kazushinjo/Shonan_lite-PI4/pi4/docs/images/home_illustrated_langstone.png

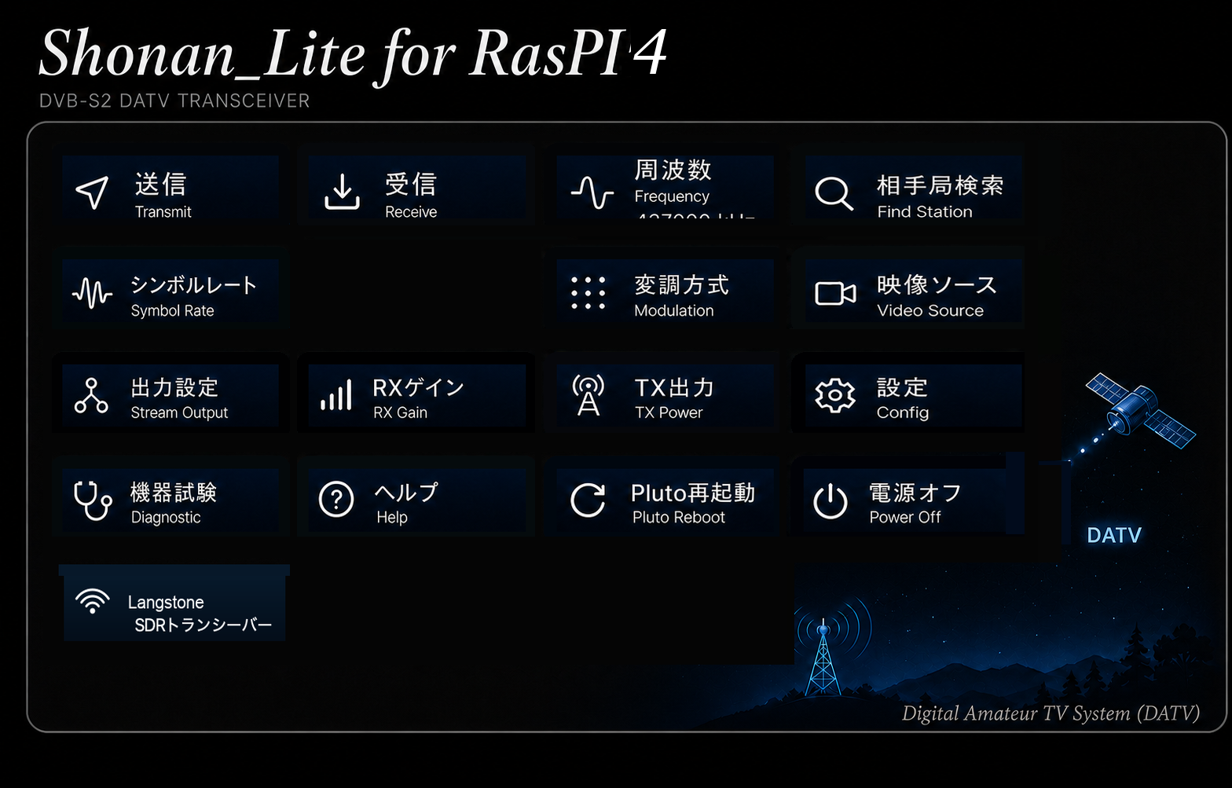
pi4/docs/images/home_illustrated_langstone.png
