kazushinjo/Shonan_lite-PI4/pi4/docs/images/home_illustrated_mockup.png

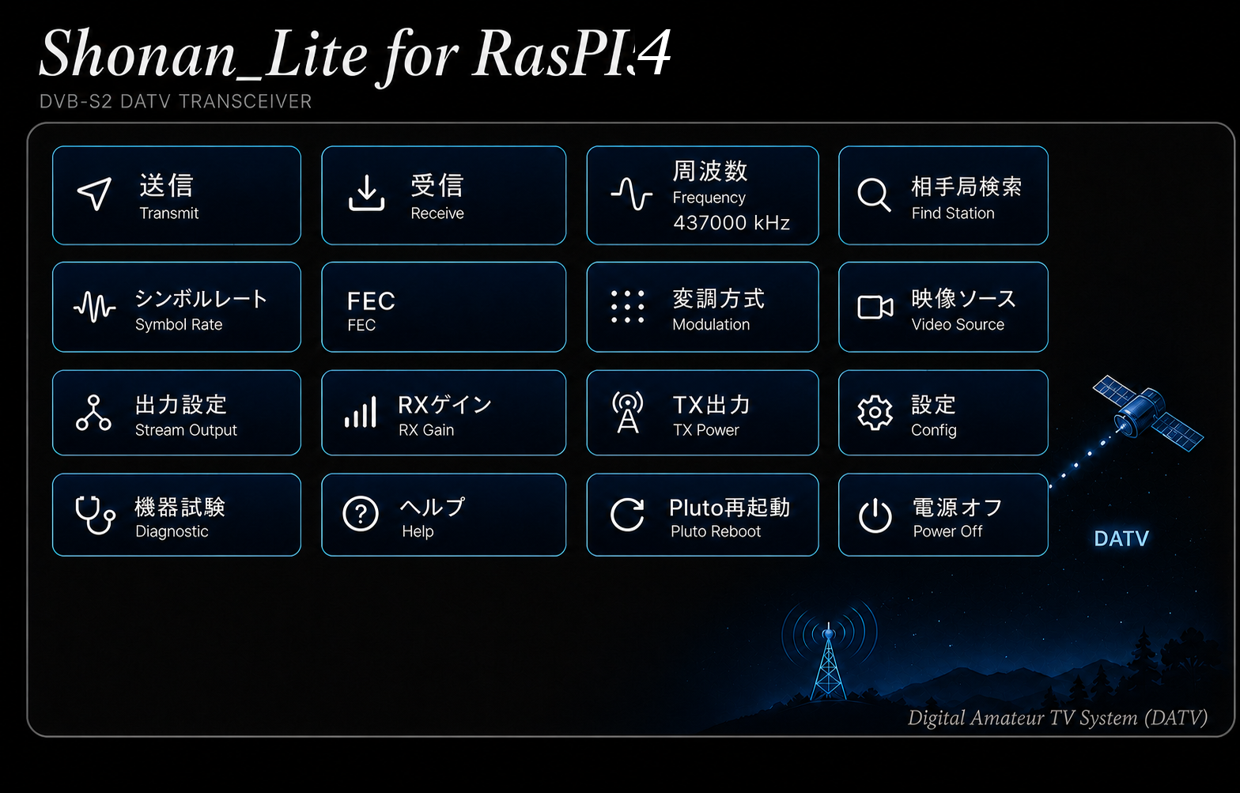
pi4/docs/images/home_illustrated_mockup.png
