kazushinjo/Shonan_lite-PI4/pi4/docs/images/screenshot_keyboard.png

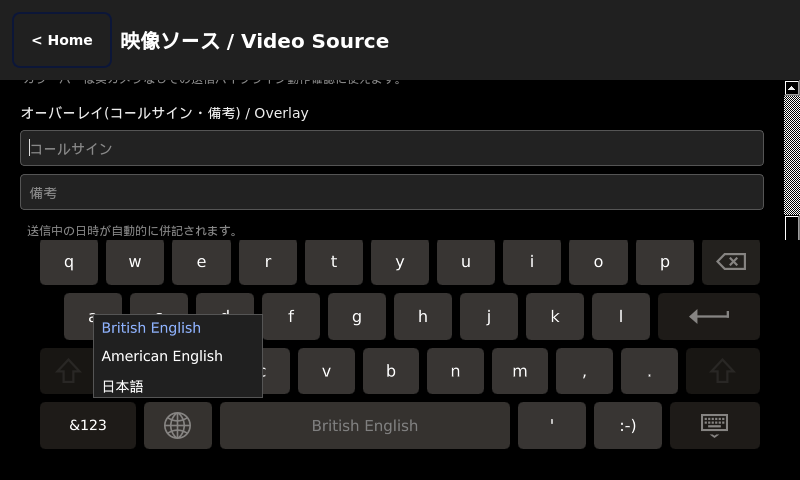
pi4/docs/images/screenshot_keyboard.png
