kazushinjo/Shonan_lite-PI4/pi4/docs/images/screenshot_overlay.png

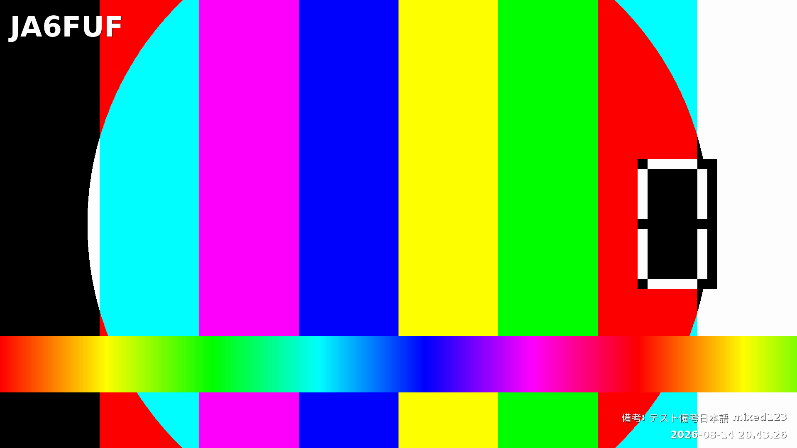
pi4/docs/images/screenshot_overlay.png
