kazushinjo/Shonan_lite-PI4/hardware/W5500_PA_PTT_Control/fabrication/assembly/w5500-esp32_3D_top_全部品.png

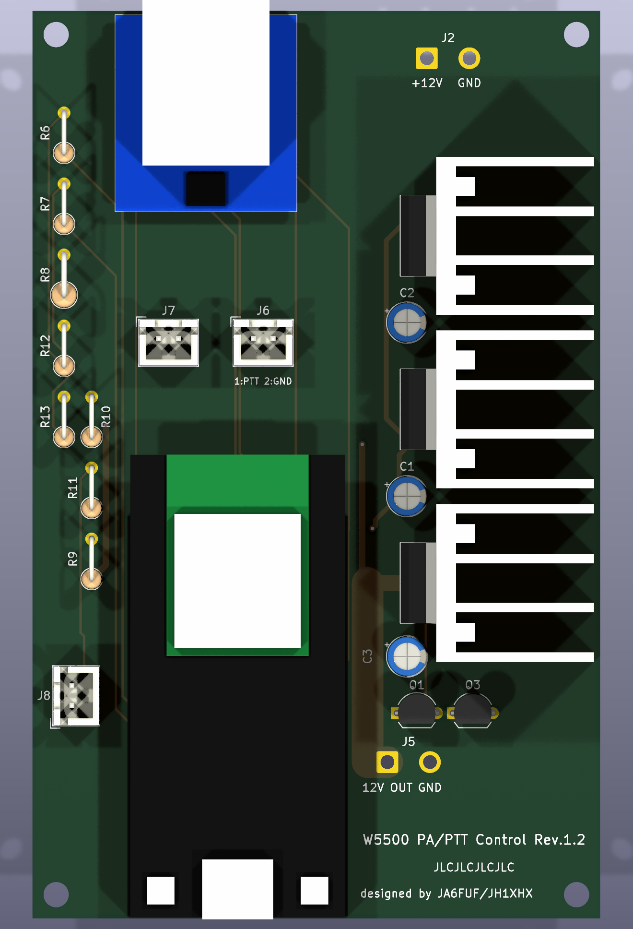
hardware/W5500_PA_PTT_Control/fabrication/assembly/w5500-esp32_3D_top_全部品.png
