kazushinjo/Shonan_lite-PI4/pi4/docs/images/test1_langstone.png

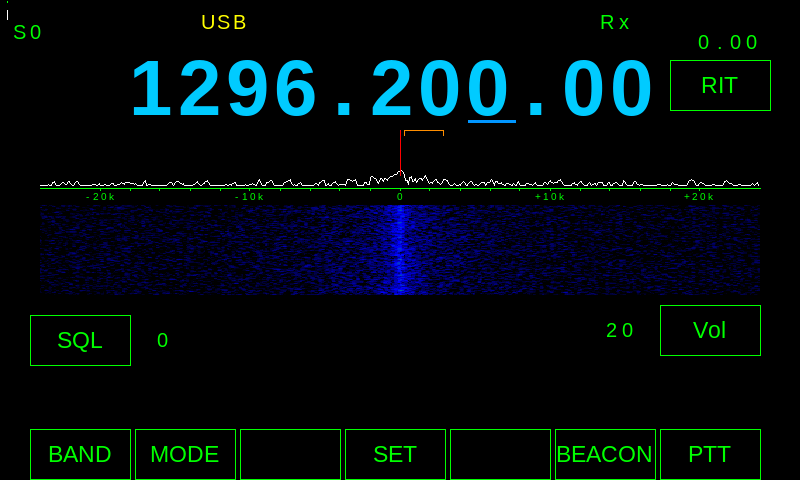
pi4/docs/images/test1_langstone.png
