kazushinjo/Shonan_lite-PI4/pi4/gui/backend.py

"""TX/RXバックエンドプロセス管理。

TX: ffmpeg映像ソース → UDP-TS(MPEG-TS over UDP、ポート8282)でPluto+上の
`udpts.sh`(`/www/settings.txt`を読み、`tsp | pluto_dvb`のパイプで変調・送出する
常駐スクリプト)へ直接プッシュする方式。開始直前にSSHで`/www/settings.txt`へ
freq/mod/sr/fec等を書き込み、udpts.shのループがそれを読み直して`pluto_dvb`を
正しいパラメータで再起動するのを待ってからffmpegを起動する。

旧SSH直接パイプ方式のコードは削除。旧`shonan_tx`(aff3ct、pi4/src/tx_main.cpp)も
GUIから呼ばない(BBHEADER CRC8の不具合が未解決のため)。

RX: shonan_rx.py(+ffplay)をQProcessで起動/停止し、標準エラー出力の状態行を
正規表現でパースしてQt Signalで通知する。
"""
from __future__ import annotations

import concurrent.futures
import http.client
import ipaddress
import os
import re
import shlex
import signal
import socket
import subprocess
import urllib.error
import urllib.request
from pathlib import Path
from typing import Optional

from PyQt5 import QtCore

from settings_store import (
    RX_SUPPORTED_MODCODS, TX_AUDIO_BITRATE_BPS, TX_SUPPORTED_MODCODS,
    TX_VIDEO_BITRATE_BPS, AppSettings,
)

PI4_DIR = Path(__file__).resolve().parent.parent  # .../pi4
# ★以前はpi4リポジトリの隣にShonan_Lite-android由来の"android"ディレクトリが
# チェックアウトされている前提のパスだったが、pi4は独立リポジトリで自己完結して
# いないと実機で参照できない(2026-08-20実機検証で発覚)。画像自体をpi4配下に
# 複製して依存を切った。
ANDROID_TEST_PATTERN = Path(__file__).resolve().parent / "assets" / "test_pattern.png"

# Pluto+上でudpts.shが`tsp -I ip 0.0.0.0:8282`として常駐待ち受けするUDP-TSポート
# (udpts.sh参照、ファームウェア固定値)。
PLUTO_UDP_TS_PORT = 8282
# PlutoのiiodがLISTENするTCPポート(ファームウェア固定値)。Windows版と同じく、
# GET /pluto.phpの200応答だけでは同一LAN上の無関係なHTTPサーバ(ルーター管理画面等)
# を誤検出するため、iiodの応答も合わせて要求して判定を厳格化する。
PLUTO_IIOD_PORT = 30431
# Windows版discover_pluto_ip()と同じ安全上限: /23より広いネットワークは
# 走査対象ホスト数が多すぎるためスキャンしない。
_DISCOVERY_MAX_SCAN_HOST_BITS = 9
# ffmpeg自身の進捗表示行("frame=  150 fps=...")の出現をもって「実際に符号化・
# 送出できている」とみなす(udpts.sh側のpluto_dvbのUnderflow等はPi4側から見えない)。
_TX_STREAMING_RE = re.compile(r"frame=\s*\d+")
# 送信画面の統計用: ffmpeg進捗行のフレーム数と、1番目の出力(UDP-TS)の累計サイズ。
# サイズを1316バイト(UDP 1パケット=TS 7パケット)で割って送出UDPパケット数とする。
_TX_PROGRESS_RE = re.compile(r"frame=\s*(\d+).*?L?size=\s*(\d+)(KiB|kB|MiB|MB|B)?")
_TX_SIZE_UNITS = {None: 1, "B": 1, "kB": 1000, "KiB": 1024, "MB": 1000 ** 2, "MiB": 1024 ** 2}
_UDP_TS_PACKET_BYTES = 1316
# 送信音声のALSAカード番号を固定値で持たない理由:
# 機体交換(046d:0825→046d:08e5)でC920がcard 0→card 1に変わった実績があり、USB抜き差しや
# 接続順序でも変わりうる(real_pluto_bringup_status.md参照)。TX開始のたびに検出する。
_CAMERA_AUDIO_ALSA_NAME_HINT = "C920"
# RX受信音声の再生に使うUSBオーディオ(カード番号はUSB抜き差しや接続順序で変わりうるため
# 固定せず、_detect_playback_alsa_device()で"USB"を含む名前から動的検出する)。
_PLAYBACK_ALSA_NAME_HINT = "USB"


def _detect_playback_alsa_device() -> Optional[str]:
    """`aplay -l`からUSBオーディオの再生カード番号を動的検出する。見つからない場合は
    Noneを返す(RX側は音声出力なしで映像のみ継続する)。"""
    try:
        result = subprocess.run(
            ["aplay", "-l"], capture_output=True, text=True, timeout=3)
    except (OSError, subprocess.TimeoutExpired):
        return None
    for line in result.stdout.splitlines():
        m = re.match(r"card (\d+):.*device (\d+):", line)
        if not m:
            continue
        if _PLAYBACK_ALSA_NAME_HINT in line:
            return f"plughw:{m.group(1)},{m.group(2)}"
    return None


def _list_capture_alsa_devices() -> list[tuple[int, str, str]]:
    """`arecord -l`の録音デバイスを(カード番号, "plughw:カード,デバイス", 行)の形で返す。"""
    try:
        result = subprocess.run(
            ["arecord", "-l"], capture_output=True, text=True, timeout=3)
    except (OSError, subprocess.TimeoutExpired):
        return []
    devices = []
    for line in result.stdout.splitlines():
        m = re.match(r"card (\d+):.*device (\d+):", line)
        if m:
            devices.append((int(m.group(1)), f"plughw:{m.group(1)},{m.group(2)}", line))
    return devices


def _usb_device_dir(sysfs_device_link: str) -> Optional[str]:
    """sysfsの`device`リンク(USBインターフェース、例: .../1-1/1-1:1.0)から、
    それが属するUSB機器のディレクトリ(.../1-1)を返す。"""
    try:
        interface_dir = os.path.realpath(sysfs_device_link)
    except OSError:
        return None
    if ":" not in os.path.basename(interface_dir):
        return None
    return os.path.dirname(interface_dir)


def _camera_alsa_card(camera_device: str, captures: list[tuple[int, str, str]]) -> Optional[int]:
    """送信に使うカメラ(v4l2)と同じUSB機器に載っている録音カードの番号を返す。

    C920は機体によって「USB PnP Sound Device」のような汎用名で列挙され、USBオーディオと
    名前で区別できないため、まずsysfs上で映像デバイスと同じUSB機器かどうかで判定し、
    分からない場合だけ名前("C920")で探す。"""
    video_name = os.path.basename(os.path.realpath(camera_device))
    camera_usb = _usb_device_dir(f"/sys/class/video4linux/{video_name}/device")
    if camera_usb is not None:
        for card, _device, _line in captures:
            if _usb_device_dir(f"/sys/class/sound/card{card}/device") == camera_usb:
                return card
    for card, _device, line in captures:
        if _CAMERA_AUDIO_ALSA_NAME_HINT in line:
            return card
    return None


def _detect_tx_audio_alsa_device(settings: AppSettings) -> Optional[str]:
    """設定画面で選んだ送信音声の入力(tx_audio_input)の録音デバイスを返す。
    camera=カメラ内蔵マイク、usb=カメラ以外の録音デバイス(USBオーディオ)。
    見つからない場合はNone(送信側は無音で送り、映像送信は中断させない)。"""
    captures = _list_capture_alsa_devices()
    camera_card = _camera_alsa_card(settings.camera_device, captures)
    for card, device, _line in captures:
        if (card == camera_card) == (settings.tx_audio_input == "camera"):
            return device
    return None


CAMERA_CAPTURE_SIZE = "1280x720"
CAMERA_CAPTURE_FPS = "30"


def _camera_input_args(device: str) -> list[str]:
    """USBカメラの入力引数。1280x720で取り込む。

    ★C920はYUYVの1280x720が最大10fpsのため、MJPEG(1280x720で30fps)があればそちらを使う。
    サイズを指定しないとC920は640x480で開くため、送信映像(1920x1080)が粗くなる。
    1280x720に対応しない汎用カメラではサイズを指定せず、ドライバ既定の解像度で開く
    (未対応のサイズ・形式を指定するとffmpegが開始できないため)。
    """
    try:
        listing = subprocess.run(
            ["v4l2-ctl", "-d", device, "--list-formats-ext"],
            capture_output=True, text=True, timeout=3).stdout
    except (OSError, subprocess.TimeoutExpired):
        listing = ""
    formats: dict[str, set[str]] = {}
    current = None
    for line in listing.splitlines():
        fmt = re.search(r"\[\d+\]: '(\w+)'", line)
        if fmt:
            current = fmt.group(1)
            formats.setdefault(current, set())
            continue
        size = re.search(r"Size: Discrete (\d+x\d+)", line)
        if size and current:
            formats[current].add(size.group(1))
    base = ["-f", "v4l2"]
    if CAMERA_CAPTURE_SIZE in formats.get("MJPG", set()):
        return base + ["-input_format", "mjpeg", "-video_size", CAMERA_CAPTURE_SIZE,
                       "-framerate", CAMERA_CAPTURE_FPS, "-i", device]
    if any(CAMERA_CAPTURE_SIZE in sizes for sizes in formats.values()):
        return base + ["-video_size", CAMERA_CAPTURE_SIZE, "-i", device]
    return base + ["-i", device]


def _set_capture_volume(device: str, percent: int) -> None:
    """録音デバイス("plughw:カード,デバイス")のマイク録音音量(ALSAミキサーの"Mic")を設定する。
    C920・USB PnP Sound Deviceとも録音音量の項目名は"Mic Capture Volume"。"""
    m = re.match(r"plughw:(\d+),", device)
    if not m:
        return
    try:
        subprocess.run(
            ["amixer", "-c", m.group(1), "sset", "Mic", f"{percent}%"],
            capture_output=True, timeout=3,
        )
    except (OSError, subprocess.TimeoutExpired):
        pass


def _audio_input_args(settings: AppSettings) -> tuple[list[str], str, Optional[str]]:
    """ffmpegの音声入力引数、ログ表示用の説明、録音デバイス(無音ならNone)を返す。

    カメラ音声・USBオーディオのどちらも1chで録音する(C920のマイク等はステレオで
    列挙されるが、plughwが1chへ変換する)。符号化側も"-ac 1"のモノラル。"""
    device = _detect_tx_audio_alsa_device(settings)
    label = "カメラ音声" if settings.tx_audio_input == "camera" else "USBオーディオ"
    if device is not None:
        return (["-f", "alsa", "-channels", "1", "-i", device],
                f"[音声] {label} ({device}、モノラル、送信音量{settings.tx_audio_volume()}%)を送信します",
                device)
    return [
        "-f", "lavfi", "-i",
        "anullsrc=channel_layout=mono:sample_rate=48000",
    ], f"[音声] {label}が見つからないため無音で送信します", None


# コールサイン/日時/備考オーバーレイに使うフォント(shonan_lite-ipad版CameraOverlayRenderer
# のPi4移植)。DejaVu Sansは英数字用、Droid Sans Fallbackは日本語用(実機で確認した限り
# 互いに相手の文字種のグリフを含まない)。drawtextフィルタは1回の呼び出しにつき
# フォントを1つしか使えないため、コールサイン・備考はPillowで事前にPNGへ文字種ごとに
# フォントを切り替えて合成し、ffmpegのoverlayフィルタで映像へ重ねる
# (_render_overlay_image/_build_overlay_pipeline参照)。日時は英数字のみなので
# 従来通りdrawtextのライブ更新(%{localtime})を使う。
_OVERLAY_FONT = "/usr/share/fonts/truetype/dejavu/DejaVuSans-Bold.ttf"
_OVERLAY_SHADOW = "shadowcolor=black@0.8:shadowx=1:shadowy=1"
_OVERLAY_ASCII_FONT_PATH = _OVERLAY_FONT
_OVERLAY_CJK_FONT_PATH = "/usr/share/fonts/truetype/droid/DroidSansFallbackFull.ttf"
_OVERLAY_IMAGE_NAME = "shonan_overlay.png"


def _split_font_runs(text: str) -> list[tuple[str, bool]]:
    """textを(区間文字列, 日本語グリフが必要か)のリストへ分割する。"""
    runs: list[tuple[str, bool]] = []
    current = ""
    current_is_cjk: Optional[bool] = None
    for ch in text:
        is_cjk = ord(ch) >= 0x3000
        if current_is_cjk is not None and is_cjk != current_is_cjk:
            runs.append((current, current_is_cjk))
            current = ""
        current += ch
        current_is_cjk = is_cjk
    if current:
        runs.append((current, bool(current_is_cjk)))
    return runs


# 送信映像の解像度はフルHD(1920x1080)固定(Pi5版と同じ)。カメラの実キャプチャ解像度や画像ファイルの
# 寸法・縦横比に関わらず、縦横比を保って縮小/拡大し、余白は黒で埋めて1920x1080に揃える。
TX_VIDEO_WIDTH = 1920
TX_VIDEO_HEIGHT = 1080
_TX_VIDEO_SCALE_FILTER = (
    f"scale={TX_VIDEO_WIDTH}:{TX_VIDEO_HEIGHT}:force_original_aspect_ratio=decrease,"
    f"pad={TX_VIDEO_WIDTH}:{TX_VIDEO_HEIGHT}:(ow-iw)/2:(oh-ih)/2,setsar=1"
)


def _parse_color(value) -> tuple[int, int, int]:
    """"#RRGGBB"を(R, G, B)へ変換する。不正な値は白。"""
    try:
        text = str(value).lstrip("#")
        if len(text) == 6:
            return tuple(int(text[i:i + 2], 16) for i in (0, 2, 4))
    except ValueError:
        pass
    return (255, 255, 255)


def _draw_mixed_text(draw, x: int, y: int, text: str, font_size: int, align: str,
                     color: tuple[int, int, int] = (255, 255, 255)) -> None:
    """英数字と日本語が混在するtextを、区間ごとにフォントを切り替えて描画する。"""
    from PIL import ImageFont

    fonts = {
        False: ImageFont.truetype(_OVERLAY_ASCII_FONT_PATH, font_size),
        True: ImageFont.truetype(_OVERLAY_CJK_FONT_PATH, font_size),
    }
    # 影は通常黒。黒など暗い文字色では影が見えないため白っぽい影にする。
    luminance = 0.299 * color[0] + 0.587 * color[1] + 0.114 * color[2]
    shadow = (0, 0, 0, 204) if luminance >= 80 else (255, 255, 255, 204)
    runs = _split_font_runs(text)
    if align == "right":
        total_width = sum(draw.textlength(t, font=fonts[c]) for t, c in runs)
        x -= total_width
    cursor = x
    for run_text, is_cjk in runs:
        font = fonts[is_cjk]
        draw.text((cursor + 1, y + 1), run_text, font=font, fill=shadow)
        draw.text((cursor, y), run_text, font=font, fill=(*color, 255))
        cursor += draw.textlength(run_text, font=font)


def _clamp_font_size(size) -> int:
    try:
        return max(8, min(256, int(size)))
    except (TypeError, ValueError):
        return 24


def _render_overlay_image(tmp_dir: str, callsign: str, note: str,
                          callsign_size: int = 68, note_size: int = 24,
                          callsign_color: str = "#FFFFFF", note_color: str = "#FFFFFF") -> str:
    """コールサイン(左上・大)と備考(右下・小、日時のすぐ上)を1920x1080の透過PNGへ描画する。
    callsign_size/note_sizeは1920x1080上での文字サイズ(px)。"""
    from PIL import Image, ImageDraw

    img = Image.new("RGBA", (TX_VIDEO_WIDTH, TX_VIDEO_HEIGHT), (0, 0, 0, 0))
    draw = ImageDraw.Draw(img)
    if callsign:
        _draw_mixed_text(draw, 24, 24, callsign, _clamp_font_size(callsign_size), align="left",
                         color=_parse_color(callsign_color))
    if note:
        # 文字サイズに関わらず備考の下端を日時のすぐ上に揃える。
        size = _clamp_font_size(note_size)
        _draw_mixed_text(draw, TX_VIDEO_WIDTH - 24, TX_VIDEO_HEIGHT - 126 - size, note, size,
                         align="right", color=_parse_color(note_color))
    path = f"{tmp_dir}/{_OVERLAY_IMAGE_NAME}"
    img.save(path)
    return path


def _build_overlay_pipeline(
        settings: AppSettings, extra_video_filters: str = "",
        *, split_preview: bool = False) -> tuple[list[str], list[str], str, str, int]:
    """映像(カメラまたは画像ファイル)を1920x1080へ揃え、コールサイン・日時・備考を重ねる
    ffmpeg入力・フィルタ関連の引数一式を組み立てる(Shonan_Lite-RasPI5からの移植)。
    戻り値は(追加入力引数, フィルタ関連引数, 映像マップ先, プレビュー用映像マップ先, 音声入力インデックス)。
    コールサイン・備考が両方空ならオーバーレイなし(フルHDへの縮小/拡大のみ)。

    split_preview=Trueの場合、映像マップ先とプレビュー用映像マップ先に別々のラベルを返す。
    ★filter_complexの出力パッド("[vout]")は一度-mapすると消費され、送信本線とプレビュー分岐の
    2箇所で同じラベルを-mapすると"Output with label ... was already used elsewhere"で
    ffmpegが起動に失敗する。splitフィルタで複製して別ラベルを割り当てる。

    ★Pi4向けの軽量化: オーバーレイ画像(1920x1080の透過PNG)は-loopで毎フレーム読み直さず
    1枚だけ入力し、overlayのeof_action=repeatで最後のフレームを重ね続ける。Pi5版と同じ
    「-loop 1 + scale2ref」ではPi4のCPUではフルHDで0.77倍速しか出ず30fpsを保てなかったが、
    この方式では1.63倍速(実機で計測)。土台の映像は先に1920x1080へ揃えるのでscale2refは不要。

    ★時刻フォーマットはコロン("%H:%M:%S")ではなく"%H.%M.%S"を使う。drawtextの
    %{localtime\\:FORMAT}展開は最初のコロン1個だけをlocaltime関数の区切りとして
    特別扱いし、FORMAT内に更にコロンがあると引数過多の警告と共に無表示になる(実機で検証済み)。
    """
    callsign = settings.overlay_callsign.strip()
    note = settings.overlay_note.strip()
    if not callsign and not note:
        # -vfは直後の最初の出力(mpegts本線)にだけ掛かる。プレビュー分岐は"0:v"を直接-mapし、
        # 別途プレビューサイズへ縮小するので問題ない。
        video_filter = _TX_VIDEO_SCALE_FILTER
        if extra_video_filters:
            video_filter += f",{extra_video_filters}"
        return [], ["-vf", video_filter], "0:v", "0:v", 1

    image_path = _render_overlay_image(
        settings.tmp_dir, callsign, note,
        settings.overlay_callsign_font_size, settings.overlay_note_font_size,
        settings.overlay_callsign_color, settings.overlay_note_color)
    date_filter = (
        f"drawtext=fontfile={_OVERLAY_FONT}:text='%{{localtime\\:%Y-%m-%d %H.%M.%S}}':"
        f"fontsize=24:fontcolor=white:x=w-text_w-24:y=h-text_h-24:{_OVERLAY_SHADOW}"
    )
    chain = (f"[0:v]{_TX_VIDEO_SCALE_FILTER}[hd];"
             f"[hd][1:v]overlay=0:0:eof_action=repeat,{date_filter}")
    if extra_video_filters:
        chain += f",{extra_video_filters}"
    if split_preview:
        chain += "[vpre];[vpre]split=2[vout][vout2]"
        video_map, preview_map = "[vout]", "[vout2]"
    else:
        chain += "[vout]"
        video_map, preview_map = "[vout]", "[vout]"
    return ["-i", image_path], ["-filter_complex", chain], video_map, preview_map, 2


# shonan_rx.pyの標準エラー出力状態行(例: "[shonan_rx] locked=False sof=0 frame=0
# rejected=0 freq_off=0.0 packets=0 errors=0")をパースする。
_RX_STATUS_RE = re.compile(
    r"locked=(True|False) sof=(\d+) frame=(\d+) rejected=(\d+) freq_off=(-?[\d.]+) packets=(\d+) errors=(\d+)"
)
# shonan-android版RxController.ktのロック監視(500ms周期ポーリング)を参考にしつつ、
# あちらにはない「停滞したら実際にプロセスを再起動する」動作を追加(実機でRXの
# フレーム同期が固まったまま進まなくなる不具合が確認されたため)。
WATCHDOG_INTERVAL_MS = 1000
WATCHDOG_STALL_TIMEOUT_MS = 8000  # frameが8秒間進まなければ停滞とみなす


def _quote(s: str) -> str:
    return shlex.quote(s)


def _build_udp_ts_url(settings: AppSettings) -> str:
    """Pluto+上のudpts.shが`tsp -I ip 0.0.0.0:8282`で待ち受けるUDP-TS宛先URL。"""
    return f"udp://{settings.pluto_host()}:{PLUTO_UDP_TS_PORT}?pkt_size=1316"


# ---- Pluto自動検出(Shonan_Lite-RasPI5から移植) ----
def _local_ipv4_subnets() -> list[tuple[str, int]]:
    """このPi4が持つ全IPv4インタフェースの(アドレス, プレフィックス長)一覧。

    Windows版と同じくpsutilが使えれば全インタフェースを列挙するが、Pi4側も
    psutilが無い場合は、UDP connect()のトリックで既定ルートの1本
    (家庭/現場運用で一般的な/24 LANと仮定)のみを返すフォールバックになる。
    """
    try:
        import psutil
        subnets = []
        for addrs in psutil.net_if_addrs().values():
            for addr in addrs:
                if addr.family != socket.AF_INET or not addr.netmask:
                    continue
                if addr.address.startswith("127.") or addr.address.startswith("169.254."):
                    continue
                prefix = sum(bin(int(octet)).count("1") for octet in addr.netmask.split("."))
                subnets.append((addr.address, prefix))
        if subnets:
            return subnets
    except Exception:
        pass
    try:
        with socket.socket(socket.AF_INET, socket.SOCK_DGRAM) as probe:
            probe.connect(("8.8.8.8", 80))
            return [(probe.getsockname()[0], 24)]
    except OSError:
        return []


def _probe_pluto(host: str, timeout: float) -> Optional[str]:
    """GET /pluto.phpの200応答に加え、iiod待受ポート(TCP)が実際に開いている
    ことも要求し、無関係なHTTPサーバの誤検出を防ぐ(Windows版と同じ判定)。
    """
    try:
        request = urllib.request.Request(f"http://{host}/pluto.php", method="GET")
        with urllib.request.urlopen(request, timeout=timeout) as response:
            if not (200 <= response.status < 300):
                return None
    except (OSError, ValueError):
        return None
    try:
        with socket.create_connection((host, PLUTO_IIOD_PORT), timeout=timeout):
            return host
    except OSError:
        return None


def discover_pluto_ip(*, timeout: float = 0.3, max_workers: int = 64) -> Optional[str]:
    """自機の全IPv4インタフェース配下でPluto+(Web UI応答+iiod待受の両方)を探す。

    Windows版discover_pluto_ip()の移植。Pluto+はPi4の既定ルートとは別の
    USB Ethernetアダプタに直結されることもあるため、_local_ipv4_subnets()で
    得られる全サブネットを走査する。
    """
    candidates: set[str] = set()
    for local_ip, prefix_len in _local_ipv4_subnets():
        host_bits = 32 - prefix_len
        if host_bits < 1 or host_bits > _DISCOVERY_MAX_SCAN_HOST_BITS:
            prefix_len = 24  # 想定外の範囲(検出失敗/広すぎるネットワーク)は/24にフォールバック
        network = ipaddress.ip_network(f"{local_ip}/{prefix_len}", strict=False)
        candidates.update(str(ip) for ip in network.hosts() if str(ip) != local_ip)
    if not candidates:
        return None

    with concurrent.futures.ThreadPoolExecutor(max_workers=max_workers) as executor:
        results = [
            host for host in executor.map(
                lambda h: _probe_pluto(h, timeout), candidates)
            if host
        ]
    if not results:
        return None
    return min(results, key=lambda ip: ipaddress.ip_address(ip))


def check_pluto_connection(settings: AppSettings) -> tuple[bool, str]:
    """IIOコンテキスト接続だけを確認し、RF設定は変更しない。"""
    try:
        settings.pluto_host()
        result = subprocess.run(
            ["iio_info", "-u", settings.pluto_uri],
            capture_output=True, text=True, timeout=5,
        )
    except (OSError, ValueError, subprocess.TimeoutExpired) as exc:
        return False, str(exc)
    if result.returncode != 0:
        detail = (result.stderr or result.stdout).strip().splitlines()
        return False, detail[-1] if detail else f"iio_info終了コード={result.returncode}"
    return True, "IIOコンテキスト接続OK"


def _uses_software_loopback(settings: AppSettings) -> bool:
    """RFループバック指定時はPlutoへ送るため、ソフトウェアループを選ばない。"""
    return settings.is_loopback() and not settings.rf_loopback_enabled


def _push_pluto_settings(settings: AppSettings, lo_hz: float) -> None:
    """SSHでPluto+の`/www/settings.txt`へDVB-S2パラメータを書き込む。

    udpts.sh(常駐shループ)は毎周回settings.txtを読み直して`pluto_dvb`を
    正しいパラメータで再起動するため、ffmpeg側のUDP-TS送出を始める前にこれを
    呼んでおく必要がある(呼ばないとPlutoが直前の周波数/シンボルレートのまま
    変調し続け、RXが一切ロックしない)。FEC値はudpts.sh側の`pluto_dvb`引数と
    同じく"/"を除いた表記(例: "3/5"→"35")で送る。pilots/frame/rolloff等
    shonan_rx.py側にも対応する設定項目がない値は両者で固定の既定値に揃える
    (pilots=On, frame=LongFrame, rolloff=0.35)。
    """
    # 430MHz帯では438.200MHzのような小数MHzを使用するため、整数化しない。
    freq_mhz = f"{lo_hz / 1_000_000:.3f}"
    symbol_rate_ksps = round(settings.symbol_rate_msps * 1000)
    fec_field = settings.fec_rate.replace("/", "")
    power = str(int(settings.tx_power_db))
    settings_text = "".join((
        f"callsign NOCALL\n",
        f"freq {freq_mhz}\n",
        "channel Custom\n",
        "mode DVBS2\n",
        f"mod {settings.modulation_scheme}\n",
        f"sr {symbol_rate_ksps}\n",
        "srselect 2000\n",
        f"fec {fec_field}\n",
        "pilots On\n",
        "frame LongFrame\n",
        f"power {power}\n",
        "rolloff 0.35\n",
        "pcrpts 800\n",
        "patperiod 200\n",
        "h265box \ncodec \nsound \naudioinput \nremux 0\n",
        "trvlo 0\ntrvloselect 0\nprovname shonan\n",
    ))
    # Write the file directly; the firmware's save.php is intentionally not used.
    ssh_command = [
        "sshpass", "-p", "analog", "ssh",
        "-o", "StrictHostKeyChecking=accept-new",
        "-o", "ConnectTimeout=6",
        "-o", "PreferredAuthentications=password",
        "-o", "PubkeyAuthentication=no",
        f"root@{settings.pluto_host()}", "tee", "/www/settings.txt",
    ]
    result = subprocess.run(
        ssh_command, input=settings_text, capture_output=True, text=True, timeout=10)
    if result.returncode != 0:
        detail = (result.stderr or result.stdout).strip()
        raise OSError(f"Pluto設定ファイル書き込み失敗: {detail or result.returncode}")


def _send_ptt_request(host: str, state: str) -> None:
    """PA_Power/PTTコントローラ(ESP32+W5500、hardware/W5500_PA_PTT_Control)へ
    TX開始/終了を通知する(`GET /tx?state=on|off`)。Pi5版と同じ経路。

    ESP32側はこのリクエストのハンドラ内でPTT(GPIO27)のON/OFFのみを行う
    (12V電源には触れない)。未接続・応答なしの場合は例外をそのまま送出する
    (呼び出し側でログのみに握りつぶし、TX本体の動作は妨げない)。
    """
    url = f"http://{host}/tx?state={state}"
    urllib.request.urlopen(url, timeout=1.5).close()


# Pi4本体のTX出力GPIO。Langstone V2のTx Output(wiringPi 29=GPIO21=物理40番ピン、
# 送信中HIGH)と同じピンに揃え、ESP32+W5500(PA_Power/PTTコントローラ)なしでも
# PA/LNA切替用のPTT ON信号を取り出せるようにする。
PI_TX_GPIO = 21


def _set_pi_tx_gpio(on: bool) -> None:
    """Pi4本体のTX出力GPIO(PI_TX_GPIO)をHIGH(送信中)/LOW(受信)にする。

    ★ラインをclaimするとLangstone側と取り合いになる可能性があるため、ラインを
    保持しない`pinctrl set`で直接書き込む。Pi以外の環境などでpinctrlが無い・
    失敗した場合は例外をそのまま送出する(呼び出し側でログのみ)。
    """
    subprocess.run(
        ["pinctrl", "set", str(PI_TX_GPIO), "op", "dh" if on else "dl"],
        check=True, timeout=2, capture_output=True,
    )


# ESP32ファームウェア(hardware/W5500_PA_PTT_Control.ino)のPIN_OUTインデックスに対応。
PTT_CHANNEL_POWER = 0  # GPIO26: 12V電源(2SJ334ハイサイドスイッチ)
PTT_CHANNEL_PTT = 1    # GPIO27: PTT


def _send_ptt_channel_state(host: str, idx: int, state: str) -> None:
    """PA_Power/PTTコントローラ(ESP32+W5500)の個別チャンネルを明示的にON/OFFする
    (`GET /ch?idx=<idx>&state=on|off`)。

    Shonan_Lite-pi4(pi4/gui)アプリ本体の起動/終了に連動したGPIO26(12V電源、
    idx=PTT_CHANNEL_POWER)制御に使う。未接続・応答なしの場合は例外をそのまま
    送出する(呼び出し側でログのみに握りつぶす)。
    """
    url = f"http://{host}/ch?idx={idx}&state={state}"
    urllib.request.urlopen(url, timeout=1.5).close()


def _terminate_process_group(process: QtCore.QProcess, sig: int) -> None:
    """QProcess.terminate()/kill()は直接の子(bash -c '...')にしか届かず、
    パイプで繋いだffmpeg/shonan_tx等の孫プロセスには届かない(bashが死んでも
    孤児として実行され続け、送信/受信が止まらない)。start()側でsetsidを使い
    bashをプロセスグループリーダーにしているため、そのグループ全体へ送る。"""
    pid = int(process.processId())
    if pid <= 0:
        return
    try:
        os.killpg(pid, sig)
    except ProcessLookupError:
        pass


class TxController(QtCore.QObject):
    status_updated = QtCore.pyqtSignal(dict)  # {"connected": bool}
    log_line = QtCore.pyqtSignal(str)
    error = QtCore.pyqtSignal(str)
    stopped = QtCore.pyqtSignal()
    video_frame = QtCore.pyqtSignal(bytes, int, int)

    def __init__(self, parent=None):
        super().__init__(parent)
        self._process: Optional[QtCore.QProcess] = None
        self._connected = False
        self._tx_frames = 0
        self._tx_packets = 0
        self._pending_lines: list[str] = []
        self._status_dirty = False
        self._quiet_mode = False
        # ウォッチドッグ再接続用。stop()が呼ばれていないのにプロセスが
        # 終了したら再起動する。
        self._should_be_running = False
        self._last_settings: Optional[AppSettings] = None
        self._last_mode: Optional[str] = None  # "video" | "camera_audio"
        # 送信中の録音デバイス(無音送信ならNone)。送信中の送信音量変更に使う。
        self._tx_audio_device: Optional[str] = None
        self._emit_timer = QtCore.QTimer(self)
        self._emit_timer.setInterval(500)
        self._emit_timer.timeout.connect(self._flush_pending_output)
        # カメラ送信中に「実際に送出している映像」を送信画面へプレビュー表示するための
        # バッファ。TX本体のffmpegプロセス自身に2つ目の出力(rawvideo→pipe:1)を追加し、
        # 同じプロセスのstdoutから直接読む(別プロセスでFIFOを読む方式は、そのプロセスが
        # 何らかの理由で予期せず終了した際にFIFOの書き手側が永久にブロックし送信全体が
        # 止まる不具合が実機で確認されたため採用しない)。
        self._preview_buffer = bytearray()
        self._preview_width = 320
        self._preview_height = 180

    def _apply_tx_audio_volume(self, settings: AppSettings) -> None:
        if self._tx_audio_device is not None:
            _set_capture_volume(self._tx_audio_device, settings.tx_audio_volume())

    def set_tx_audio_volume(self, percent: int) -> bool:
        """送信中の録音デバイスの送信音量を即時変更する。無音送信中(デバイスなし)はFalse。"""
        if self._tx_audio_device is None:
            return False
        _set_capture_volume(self._tx_audio_device, percent)
        return True

    def is_running(self) -> bool:
        return self._process is not None and self._process.state() != QtCore.QProcess.NotRunning

    def get_status(self) -> dict:
        """quiet_mode(カメラ+音声診断)中はstatus_updatedを発行しないため、呼び出し側は
        これをポーリングして状態を読む(refresh_camera_audio_frame_counts()が併せて
        _connectedも更新する)。"""
        return {"connected": self._connected}

    def _launch_ffmpeg(self, args: list, *, output_file: Optional[str] = None,
                       preview_output: bool = False) -> None:
        proc = QtCore.QProcess(self)
        proc.setProgram("ffmpeg")
        proc.setArguments(args)
        # プレビュー分岐時だけstdoutをrawvideo、stderrを進捗ログとして分離する。
        # それ以外はffmpegの進捗表示がstderrに出るため、stdoutと合流させて一本化する。
        proc.setProcessChannelMode(
            QtCore.QProcess.SeparateChannels if preview_output
            else QtCore.QProcess.MergedChannels
        )
        # ★QProcessが既定でstdinを親と繋がった開いたままのパイプにしてしまい、
        # v4l2カメラ+ALSA同時キャプチャがそれに引きずられて断続的な不具合を起こすことが
        # 実機検証で判明した(real_pluto_bringup_status.md参照)。明示的にnullDeviceへ。
        proc.setStandardInputFile(QtCore.QProcess.nullDevice())
        if output_file:
            proc.setStandardOutputFile(output_file)
        elif preview_output:
            proc.readyReadStandardError.connect(lambda: self._on_output(proc, stderr=True))
            proc.readyReadStandardOutput.connect(lambda: self._on_preview_output(proc))
        else:
            proc.readyReadStandardOutput.connect(lambda: self._on_output(proc))
        proc.finished.connect(self._on_finished)
        proc.start()
        self._process = proc
        if not output_file:
            self._emit_timer.start()

    def start(self, settings: AppSettings) -> None:
        if self.is_running():
            return
        if not settings.tx_mod_cod_supported():
            self.error.emit(
                f"未対応のMod-Cod組み合わせです: {settings.mod_cod()}\n"
                f"対応組み合わせ: {', '.join(TX_SUPPORTED_MODCODS)}"
            )
            return
        lo_hz = settings.effective_lo_hz()
        if lo_hz is None:
            self.error.emit("周波数が未設定です(ループバック試験を選択中はFrequency画面で手動設定してください)")
            return
        if settings.lnb_active():
            self.error.emit("LNB使用中は送信できません(受信専用)。周波数画面でLNBをOFFにしてください")
            return

        self._last_settings = settings
        self._last_mode = "video"
        self._should_be_running = True
        self._connected = False
        self._tx_frames = 0
        self._tx_packets = 0
        self._pending_lines = []
        self._status_dirty = False
        self._quiet_mode = False

        if settings.use_color_bar_source or settings.video_source == "colorbar":
            # Android版ColorBarSourceと同じ1920x1080固定画像を30fpsで反復する。
            video_args = [
                "-re", "-loop", "1", "-framerate", "30",
                "-i", str(ANDROID_TEST_PATTERN),
            ]
            # ★カラーバー画像自体に既にコールサインが描かれているため焼き込まない
            # (shonan_lite-ipad版VideoSourceSettingsViewと同じ扱い)。
            overlay_input_args: list[str] = []
            overlay_filter_args: list[str] = ["-vf", _TX_VIDEO_SCALE_FILTER]
            video_map = preview_video_map = "0:v"
            audio_index = 1
        elif settings.video_source == "file" and settings.video_file_path:
            # ★選択できるのは静止画のみ(videosource.py参照)。カラーバーと同じ「-loop 1 -framerate 30」で
            # 静止画を反復送信し、カメラと同じくコールサイン・備考を重ねる(Pi5版と同じ)。
            video_args = [
                "-re", "-loop", "1", "-framerate", "30",
                "-i", settings.video_file_path,
            ]
            overlay_input_args, overlay_filter_args, video_map, preview_video_map, audio_index = \
                _build_overlay_pipeline(settings, split_preview=True)
        else:
            video_args = _camera_input_args(settings.camera_device)
            overlay_input_args, overlay_filter_args, video_map, preview_video_map, audio_index = \
                _build_overlay_pipeline(settings, split_preview=True)

        # カメラ送信中は「実際に送出している映像」を送信画面へプレビュー表示する。
        # ★プレビュー分岐は本線と別のラベル(preview_video_map)を-mapする(同じ[vout]を2回
        # -mapするとffmpegが起動に失敗する)。
        preview_enabled = settings.video_source == "camera" and not settings.use_color_bar_source
        self._preview_buffer.clear()

        video_kbps = TX_VIDEO_BITRATE_BPS // 1000
        audio_kbps = TX_AUDIO_BITRATE_BPS // 1000
        if _uses_software_loopback(settings):
            output_url = f"udp://{settings.effective_loopback_host()}:{settings.rx_listen_port}?pkt_size=1316"
        else:
            try:
                _push_pluto_settings(settings, lo_hz)
            except OSError as exc:
                self.error.emit(f"Pluto+設定送信に失敗しました: {exc}")
                return
            output_url = _build_udp_ts_url(settings)
        if settings.use_on_device_demod:
            # ★オンデバイス復調はアッテネータ経由の自己受信試験でPAを使わない。PTT ONで
            # オーディオアンプの電源が切れ、受信音を聞けなくなるため、PTTはOFFのまま送信する
            # (stop()側のOFF通知は従来どおり送り、OFFを保証する)。
            self.log_line.emit("[PTT] オンデバイス復調中のためPTTをONにせず送信します")
        else:
            try:
                _set_pi_tx_gpio(True)
            except (OSError, subprocess.SubprocessError) as exc:
                self.log_line.emit(f"[PTT] Pi4 GPIO{PI_TX_GPIO}のHIGH出力に失敗しました: {exc}")
            if settings.active_ptt_controller_host():
                try:
                    _send_ptt_request(settings.active_ptt_controller_host(), "on")
                except (OSError, urllib.error.URLError, http.client.HTTPException) as exc:
                    self.log_line.emit(f"[PTT] ESP32への送信開始通知に失敗しました: {exc}")
        # 設定画面で選んだ音声入力(カメラ音声/USBオーディオ、無ければ無音)をAACで
        # 映像と一緒に送信する(Pi5版と同じ)。
        audio_args, audio_message, self._tx_audio_device = _audio_input_args(settings)
        self._apply_tx_audio_volume(settings)
        self.log_line.emit(audio_message)
        args = video_args + overlay_input_args + audio_args + overlay_filter_args + [
            "-map", video_map, "-map", f"{audio_index}:a",
            # Raspberry Pi 4のVideoCore H.264ハードウェアエンコーダを使用する。
            # dump_extraで各キーフレームへSPS/PPSを付加し、途中視聴でも復号可能にする。
            "-c:v", "h264_v4l2m2m", "-bf", "0",
            "-bsf:v", "dump_extra=freq=keyframe",
            "-b:v", f"{video_kbps}k", "-maxrate", f"{video_kbps}k", "-bufsize", f"{video_kbps}k",
            "-g", "30", "-pix_fmt", "yuv420p",
            # 16kbpsを左右2chで分け合うと音質が落ちるため、声の送信はモノラルに固定する。
            "-c:a", "aac", "-ac", "1", "-b:a", f"{audio_kbps}k",
            "-f", "mpegts", output_url,
        ]
        if preview_enabled:
            args = args + [
                "-map", preview_video_map, "-an", "-c:v", "rawvideo", "-pix_fmt", "rgb24",
                "-s", f"{self._preview_width}x{self._preview_height}", "-r", "5",
                "-f", "rawvideo", "pipe:1",
            ]
        self._launch_ffmpeg(args, preview_output=preview_enabled)

    def _on_preview_output(self, proc: QtCore.QProcess) -> None:
        self._preview_buffer.extend(bytes(proc.readAllStandardOutput()))
        frame_size = self._preview_width * self._preview_height * 3
        while len(self._preview_buffer) >= frame_size:
            frame = bytes(self._preview_buffer[:frame_size])
            del self._preview_buffer[:frame_size]
            self.video_frame.emit(frame, self._preview_width, self._preview_height)

    def stop(self) -> None:
        self._should_be_running = False
        was_running = self.is_running()
        # ★Pi4 GPIOはローカルで軽いため、起動途中で失敗した場合もHIGHのまま
        # 残さないよう、送信中かどうかにかかわらずLOWへ戻す。
        try:
            _set_pi_tx_gpio(False)
        except (OSError, subprocess.SubprocessError) as exc:
            if was_running:
                self.log_line.emit(f"[PTT] Pi4 GPIO{PI_TX_GPIO}のLOW出力に失敗しました: {exc}")
        if was_running and self._last_settings and self._last_settings.active_ptt_controller_host():
            try:
                _send_ptt_request(self._last_settings.active_ptt_controller_host(), "off")
            except (OSError, urllib.error.URLError, http.client.HTTPException) as exc:
                self.log_line.emit(f"[PTT] ESP32への送信終了通知に失敗しました: {exc}")
        if not was_running:
            return
        # ffmpegを直接起動している(setsid/bash -cのパイプ構成をやめた)ため、QProcessの
        # terminate()/kill()がそのままffmpeg本体に届く。
        self._process.terminate()
        QtCore.QTimer.singleShot(5000, self._force_kill_if_still_running)

    def _force_kill_if_still_running(self) -> None:
        if self.is_running():
            self._process.kill()

    def _on_output(self, proc: QtCore.QProcess, *, stderr: bool = False) -> None:
        # ★行ごとにシグナルを同期発行せず、いったんバッファに溜めるだけにする
        # (start_camera_audio()実行中のquiet_modeではそもそもこのハンドラ自体を使わない)。
        # 実際の発行は_flush_pending_output()。
        channel = proc.readAllStandardError() if stderr else proc.readAllStandardOutput()
        data = bytes(channel).decode("utf-8", errors="replace")
        for line in data.splitlines():
            print(f"[tx] {line}", flush=True)
            self._pending_lines.append(line)
            if not self._connected and _TX_STREAMING_RE.search(line):
                self._connected = True
                self._status_dirty = True
            progress = _TX_PROGRESS_RE.search(line)
            if progress:
                self._tx_frames = int(progress.group(1))
                size_bytes = int(progress.group(2)) * _TX_SIZE_UNITS.get(progress.group(3), 1)
                self._tx_packets = size_bytes // _UDP_TS_PACKET_BYTES
                self._status_dirty = True

    def _flush_pending_output(self) -> None:
        if self._pending_lines:
            lines, self._pending_lines = self._pending_lines, []
            for line in lines:
                self.log_line.emit(line)
        if self._status_dirty:
            self._status_dirty = False
            self.status_updated.emit({
                "connected": self._connected,
                "packets": self._tx_packets,
                "frames": self._tx_frames,
            })

    def _on_finished(self) -> None:
        self._emit_timer.stop()
        self._flush_pending_output()
        self._process = None
        self._preview_buffer.clear()
        if self._should_be_running and self._last_settings is not None:
            settings, mode = self._last_settings, self._last_mode
            QtCore.QTimer.singleShot(500, lambda: self._restart(settings, mode))
        else:
            self.stopped.emit()

    def _restart(self, settings: AppSettings, mode: Optional[str]) -> None:
        if not self._should_be_running:
            return
        if mode == "camera_audio":
            self.start_camera_audio(settings)
        else:
            self.start(settings)

    def start_camera_audio(self, settings: AppSettings) -> None:
        """カメラ映像+USBカメラ内蔵マイク音声を実際にキャプチャしてPluto+へ送出する経路が
        健全かを確認する診断用。Android版 CameraAudioTxDiagPipeline
        (Camera/Mic→H.264/AAC→TS Mux→Dvbs2TxPipeline)のPi4移植。

        ffmpegの showinfo/ashowinfo フィルタ(1フレームごとに1行ログを出す)を使って、
        Android版のvideoFrameCount/audioFrameCountに相当する正確なフレーム数を取得する。
        """
        if self.is_running():
            return
        if not settings.tx_mod_cod_supported():
            self.error.emit(
                f"未対応のMod-Cod組み合わせです: {settings.mod_cod()}\n"
                f"対応組み合わせ: {', '.join(TX_SUPPORTED_MODCODS)}"
            )
            return
        lo_hz = settings.effective_lo_hz()
        if lo_hz is None:
            self.error.emit("周波数が未設定です")
            return
        if settings.lnb_active():
            self.error.emit("LNB使用中は送信できません(受信専用)。周波数画面でLNBをOFFにしてください")
            return

        self._last_settings = settings
        self._last_mode = "camera_audio"
        self._should_be_running = True
        self._connected = False
        self._quiet_mode = True
        self.video_frame_count = 0
        self.audio_frame_count = 0
        self._ca_log_read_offset = 0
        # ffmpegの標準出力+標準エラー(showinfo/ashowinfoのログ含む)をファイルへ落とし、
        # get_status()/refresh_camera_audio_frame_counts()呼び出し時にポーリングで読む。
        self._ca_log_path = f"{settings.tmp_dir}/shonan_ca_ffmpeg.log"

        video_kbps = TX_VIDEO_BITRATE_BPS // 1000
        audio_kbps = TX_AUDIO_BITRATE_BPS // 1000
        # H.264/AACはPi 4で符号化し、Plutoのudpts.shはUDP-TSをそのまま変調へ渡す。
        try:
            _push_pluto_settings(settings, lo_hz)
        except OSError as exc:
            self.error.emit(f"Pluto+設定送信に失敗しました: {exc}")
            return
        udp_ts_url = _build_udp_ts_url(settings)
        overlay_input_args, overlay_filter_args, video_map, _preview_video_map, audio_index = \
            _build_overlay_pipeline(settings, extra_video_filters="showinfo")
        audio_args, _audio_message, self._tx_audio_device = _audio_input_args(settings)
        self._apply_tx_audio_volume(settings)
        args = _camera_input_args(settings.camera_device) + overlay_input_args + \
            audio_args + overlay_filter_args + [
            "-map", video_map, "-map", f"{audio_index}:a",
            "-c:v", "h264_v4l2m2m", "-bf", "0",
            "-bsf:v", "dump_extra=freq=keyframe",
            "-b:v", f"{video_kbps}k", "-maxrate", f"{video_kbps}k", "-bufsize", f"{video_kbps}k",
            "-g", "30", "-pix_fmt", "yuv420p",
            "-c:a", "aac", "-ac", "1", "-b:a", f"{audio_kbps}k", "-af", "ashowinfo",
            "-f", "mpegts", udp_ts_url,
        ]
        self._launch_ffmpeg(args, output_file=self._ca_log_path)

    def refresh_camera_audio_frame_counts(self) -> None:
        """診断中に1秒おき等で呼び、ffmpegのshowinfo/ashowinfoログファイルから
        映像/音声フレーム数を数え直し(Android版videoFrameCount/audioFrameCount相当)、
        併せて_connected(ffmpeg自身の進捗行の出現)も更新する。

        ★毎回ファイル全体を読み直して数え直す実装だと、ログが数千行に育つにつれ
        Qtイベントループを塞ぐ時間が伸びる懸念があったため(real_pluto_bringup_status.md
        参照)、前回読み取り位置以降の差分のみ読んで加算する。
        """
        log_path = getattr(self, "_ca_log_path", None)
        if not log_path or not os.path.exists(log_path):
            return
        offset = getattr(self, "_ca_log_read_offset", 0)
        try:
            with open(log_path, "r", errors="replace") as f:
                f.seek(offset)
                chunk = f.read()
                self._ca_log_read_offset = f.tell()
        except OSError:
            return
        self.video_frame_count += chunk.count("Parsed_showinfo")
        self.audio_frame_count += chunk.count("Parsed_ashowinfo")
        if not self._connected and _TX_STREAMING_RE.search(chunk):
            self._connected = True


class RxController(QtCore.QObject):
    status_updated = QtCore.pyqtSignal(dict)
    log_line = QtCore.pyqtSignal(str)
    error = QtCore.pyqtSignal(str)
    stopped = QtCore.pyqtSignal()
    video_frame = QtCore.pyqtSignal(bytes, int, int)

    def __init__(self, parent=None):
        super().__init__(parent)
        self._rx_process: Optional[QtCore.QProcess] = None
        self._ffplay_process: Optional[QtCore.QProcess] = None
        self._fifo_path: Optional[str] = None
        self._settings: Optional[AppSettings] = None
        self._last_frame_count = 0
        self._ms_since_progress = 0
        self._restart_pending = False
        self._video_buffer = bytearray()
        self._video_width = 640
        self._video_height = 360
        self._watchdog_timer = QtCore.QTimer(self)
        self._watchdog_timer.setInterval(WATCHDOG_INTERVAL_MS)
        self._watchdog_timer.timeout.connect(self._check_watchdog)

    def run_iio_preflight(self, settings: AppSettings, *, notify_error: bool = True) -> bool:
        """短いDMA読出しでPluto RX/IIOの健全性を確認する。"""
        if not settings.iio_preflight_enabled:
            self.log_line.emit("[iio-preflight] SKIPPED (disabled in settings)")
            return True
        if settings.is_loopback():
            return True
        probe_cmd = (
            "set -o pipefail; "
            f"iio_readdev -u {_quote(settings.pluto_uri)} -b 32768 "
            "cf-ad9361-lpc voltage0 voltage1 2>/tmp/shonan_iio_probe.err "
            "| head -c 4096 | wc -c"
        )
        try:
            probe = subprocess.run(
                ["bash", "-c", probe_cmd], capture_output=True,
                text=True, timeout=6)
            probe_bytes = int(probe.stdout.strip() or "0")
        except (OSError, ValueError, subprocess.TimeoutExpired):
            probe_bytes = 0
        if probe_bytes >= 4096:
            self.log_line.emit(f"[iio-preflight] OK ({probe_bytes} bytes)")
            return True
        message = (
            "Pluto RX DMAのIIOプリフライトに失敗しました。"
            "RF NO LOCKではありません。Plutoを再起動してから再試行してください。"
        )
        self.log_line.emit(f"[iio-preflight] FAILED: {message}")
        if notify_error:
            self.error.emit(message)
        return False

    def is_running(self) -> bool:
        return self._rx_process is not None and self._rx_process.state() != QtCore.QProcess.NotRunning

    def start(self, settings: AppSettings) -> None:
        if self.is_running():
            return
        if not settings.rx_mod_cod_supported():
            self.error.emit(
                f"未対応のMod-Cod組み合わせです: {settings.mod_cod()}\n"
                f"対応組み合わせ: {', '.join(RX_SUPPORTED_MODCODS)}"
            )
            return
        # ★LNB使用中は表示周波数(10GHz)ではなく、LNB局部発振を引いたIF周波数で受信する。
        lo_hz = settings.rx_tune_hz()
        if lo_hz is None:
            self.error.emit("周波数が未設定です")
            return

        # Pluto単体の再起動ではPluto側の設定が初期値へ戻るため、RX先行時も
        # 開始直前にTX/RX共通パラメータを必ず再適用する。
        try:
            _push_pluto_settings(settings, lo_hz)
        except OSError as exc:
            self.error.emit(f"Pluto設定送信に失敗しました: {exc}")
            return

        if not self.run_iio_preflight(settings):
            return

        self._settings = settings
        self._last_frame_count = 0
        self._ms_since_progress = 0
        self._restart_pending = False

        fifo_path = f"{settings.tmp_dir}/shonan_rx_gui.ts"
        self._fifo_path = fifo_path

        # ★TxControllerは_push_pluto_settings()でpilots=Onを送るため、
        # RX側も--pilotsを明示してTXと一致させる。
        # ★shonan_rx.pyの--sample-rate-hzは実IQサンプルレート(sps=2固定、
        # real_pluto_bringup_status.md参照)。symbol_rate_msps由来のsymbol_rate_hz()から
        # 2倍して求める(旧settings.sample_rate_hz固定値フィールドはsymbol_rate_msps側の
        # 実制御に一本化されたため廃止)。
        sample_rate_hz = settings.symbol_rate_hz() * 2
        rx_cmd = (
            f"rm -f {_quote(fifo_path)}; mkfifo {_quote(fifo_path)}; "
            f"python3 {PI4_DIR}/rx/shonan_rx.py --pluto-uri {_quote(settings.pluto_uri)} "
            f"--lo-hz {lo_hz} --sample-rate-hz {sample_rate_hz} "
            f"--mod-cod {_quote(settings.mod_cod())} --pilots "
            f"--agc {'--agc' if settings.rx_agc_enabled else '--no-agc'} "
            f"--gain-db {settings.rx_gain_db} --output-fifo {_quote(fifo_path)} 2>&1"
        )

        proc = QtCore.QProcess(self)
        proc.setProgram("setsid")
        proc.setArguments(["bash", "-c", rx_cmd])
        # ★TxController.start()と同じ理由でstdinを明示的にnullDeviceへ
        # (real_pluto_bringup_status.md参照。RX側では未確認だが予防的に統一する)。
        proc.setStandardInputFile(QtCore.QProcess.nullDevice())
        proc.readyReadStandardOutput.connect(lambda: self._on_output(proc))
        proc.finished.connect(self._on_finished)
        proc.start()
        self._rx_process = proc
        self._watchdog_timer.start()

        # file_sink(RX側)はFIFOをwriteでopenする際、読み手が先にいないとブロックするため
        # 少し遅らせてffmpegを起動する(pi4/scripts/run_rx_display.shと同じ理由)。
        QtCore.QTimer.singleShot(1500, lambda: self._start_ffplay(fifo_path))

    def _start_ffplay(self, fifo_path: str) -> None:
        """FIFOを1つのffmpegプロセスだけで読み、映像は生RGBフレームとしてstdoutへ
        (video_frameシグナル経由でQt側QLabelへ描画)、音声はUSBオーディオへ直接出力する
        2系統出力にする。★GUI(Qt eglfs)がKMS/DRMディスプレイを既に占有しているため、
        ffplay単体をFIFOに向けて起動する方式(外部ウィンドウ表示)は、SDL2側が
        DRMマスターを取得できずダミードライバへ無言でフォールバックし、プロセスは
        生きたまま何も表示されない不具合が実機で確認された。ffmpegでRGBへ変換して
        Qt自身の描画パイプラインに乗せることでこの競合を回避する。FIFOは1プロセス
        しか安定して読めないため、映像と音声を同じffmpeg起動から分岐させる。
        ★音声出力先を汎用エイリアス"default"にするとQProcess経由で実機がクラッシュ
        した(この機体の"default"は再生に使えないデバイスへ解決されている模様)。
        音声なしのテストパターンや映像ソースでは、音声出力を同じffmpegに追加すると
        「Output file does not contain any stream」でプロセスが終了するため、表示用は
        映像出力だけにする。"""
        if self._ffplay_process is not None or self._settings is None:
            return
        self._video_buffer.clear()
        proc = QtCore.QProcess(self)
        proc.setProgram('ffmpeg')
        args = [
            '-loglevel', 'warning', '-fflags', 'nobuffer', '-flags', 'low_delay',
            '-f', 'mpegts', '-i', fifo_path,
            '-an', '-vf', f'scale={self._video_width}:{self._video_height}',
            '-pix_fmt', 'rgb24', '-f', 'rawvideo', 'pipe:1',
        ]
        proc.setArguments(args)
        proc.readyReadStandardOutput.connect(lambda: self._on_video_output(proc))
        proc.readyReadStandardError.connect(lambda: print(
            f"[video] {bytes(proc.readAllStandardError()).decode('utf-8', errors='replace').strip()}", flush=True))
        proc.errorOccurred.connect(lambda err: print(f"[video] QProcess error: {err}", flush=True))
        proc.start()
        self._ffplay_process = proc

    def _on_video_output(self, proc: QtCore.QProcess) -> None:
        self._video_buffer.extend(bytes(proc.readAllStandardOutput()))
        frame_size = self._video_width * self._video_height * 3
        while len(self._video_buffer) >= frame_size:
            frame = bytes(self._video_buffer[:frame_size])
            del self._video_buffer[:frame_size]
            self.video_frame.emit(frame, self._video_width, self._video_height)

    def set_volume(self, percent: int) -> None:
        """Android版RxController.setVolume相当。ffmpeg(ALSA出力)を再起動せず、
        ALSAミキサー自体の音量をamixerで即時反映する(映像パイプラインの
        再起動によるIDR待ち=一瞬のフリーズを避けるため)。★USBオーディオの
        ミキサーコントロール名は"PCM"(Masterは存在しない、_start_ffplay参照)。"""
        device = _detect_playback_alsa_device()
        if device is None:
            return
        m = re.match(r"plughw:(\d+),", device)
        if not m:
            return
        try:
            subprocess.run(
                ["amixer", "-c", m.group(1), "sset", "PCM", f"{percent}%"],
                capture_output=True, timeout=3,
            )
        except (OSError, subprocess.TimeoutExpired):
            pass

    # ユーザー操作による明示的な停止。ウォッチドッグによる再起動は_stop_for_restart()を使う。
    def stop(self) -> None:
        print("[rx] stop() called (user pressed Stop, or main.py shutdown)", flush=True)
        self._settings = None
        self._restart_pending = False
        self._watchdog_timer.stop()
        self._stop_process()

    def _stop_for_restart(self) -> None:
        self._watchdog_timer.stop()
        self._stop_process()

    def _stop_process(self) -> None:
        if self._ffplay_process is not None:
            # ★terminate()(SIGTERM)は非同期でありプロセスが実際に終了する保証がない。
            # ここで確実に終了させないと、RX再起動(watchdog等)のたびに同じFIFOを
            # 読む古いffmpegプロセスが生き残り、新しいffmpegと2プロセスで同一FIFOを
            # 奪い合って映像ストリームが破損する不具合が実機で確認された
            # (RXはlocked=trueでも映像が一切表示されない症状)。kill()(SIGKILL)は
            # 捕捉・無視できないため確実に終了する。
            self._ffplay_process.kill()
            self._ffplay_process = None
        self._video_buffer.clear()
        if not self.is_running():
            # ★プロセスが既に(watchdog検知前に)終了していた場合、QProcess.finishedは
            # 既に発火済みで_on_finished()もおそらく実行済みのため、ここで改めて
            # _on_finished()を呼び直し、_restart_pendingを見て再起動するかどうかを
            # 判定させる。以前はここで無条件にstopped.emit()していたため、watchdogが
            # 再起動フラグを立てた直後にプロセスが既に死んでいるタイミングと重なると、
            # 再起動されずそのまま停止してしまう不具合があった(実機で再現確認済み)。
            self._on_finished()
            return
        _terminate_process_group(self._rx_process, signal.SIGTERM)
        QtCore.QTimer.singleShot(8000, self._force_kill_if_still_running)

    def _force_kill_if_still_running(self) -> None:
        if self.is_running():
            _terminate_process_group(self._rx_process, signal.SIGKILL)

    def _check_watchdog(self) -> None:
        if not self.is_running():
            return
        self._ms_since_progress += WATCHDOG_INTERVAL_MS
        if self._ms_since_progress >= WATCHDOG_STALL_TIMEOUT_MS:
            self.log_line.emit(
                f"[watchdog] frameが{WATCHDOG_STALL_TIMEOUT_MS // 1000}秒間進まないため"
                f"RXを再起動します"
            )
            self._restart_pending = True
            self._stop_for_restart()

    def _on_output(self, proc: QtCore.QProcess) -> None:
        data = bytes(proc.readAllStandardOutput()).decode("utf-8", errors="replace")
        for line in data.splitlines():
            self.log_line.emit(line)
            print(f"[rx] {line}", flush=True)
            m = _RX_STATUS_RE.search(line)
            if m:
                frame = int(m.group(3))
                if frame != self._last_frame_count:
                    self._last_frame_count = frame
                    self._ms_since_progress = 0
                self.status_updated.emit({
                    "locked": m.group(1) == "True",
                    "sof": int(m.group(2)),
                    "frame": frame,
                    "rejected": int(m.group(4)),
                    "freq_off": float(m.group(5)),
                    "packets": int(m.group(6)),
                    "errors": int(m.group(7)),
                })

    def _on_finished(self) -> None:
        self._rx_process = None
        # ★self._settingsはstop()でのみNoneにされる。つまり「ユーザーが明示的に停止した
        # 場合」以外は理由を問わず(watchdogが停滞を検知してSIGTERMした場合はもちろん、
        # RXプロセス自体がwatchdogの検知前に予期せず終了・クラッシュした場合も含めて)
        # 常に再起動する。以前は_restart_pending(watchdogが停滞を検知した場合のみ立つ
        # フラグ)を見ていたため、プロセスが停滞検知に届く前に終了した場合(実機で
        # libiioの一時的なソケットエラー"Create socket: -113"が発生した際に再現確認済み)
        # に再起動されず、そのまま停止してしまう不具合があった。
        self._restart_pending = False
        if self._settings is not None:
            print("[rx] process ended unexpectedly (or watchdog stopped it), restarting", flush=True)
            settings = self._settings
            QtCore.QTimer.singleShot(500, lambda: self._restart_if_still_wanted(settings))
        else:
            print("[rx] stop() was called, not restarting", flush=True)
            self._watchdog_timer.stop()
            self.stopped.emit()

    def _restart_if_still_wanted(self, settings: AppSettings) -> None:
        # ★再起動待ち(500ms)の間にstop()が呼ばれた場合は再起動しない。以前は予約済みの
        # start()がそのまま実行され、停止したはずのRXが動き続けていた(機器試験の
        # 全体試験終了直後に実機で再現。送信が無いためwatchdogで約8秒ごとに再起動し続ける)。
        if self._settings is None:
            print("[rx] restart cancelled (stop() was called while waiting)", flush=True)
            return
        self.start(settings)
