kazushinjo/Shonan_lite-PI4/pi4/gui/settings_store.py

"""shonan-pi4 GUI設定の永続化。

設定は単一のJSONファイル(~/.config/shonan-pi4/settings.json)にまとめて保存する。

- Pluto+がPi4に直結のため、送信先IP/Port(別筐体への送信先)ではなく
  pluto_uri(自機からPluto+へのlibiio URI)を持つ。
- fec_rate+modulation_schemeを合成した値がshonan_tx/shonan_rx.pyへ実際に渡る
  --mod-cod になる(mod_cod()参照)。
- 送信ポート、受信ポート、シンボルレート、FEC、変調、ゲイン、出力、音量は
  いずれも実際の送受信制御に使われる。
"""
from __future__ import annotations

import json
import ipaddress
import os
import re
from dataclasses import asdict, dataclass, field
from pathlib import Path
from typing import Optional

SETTINGS_DIR = Path(os.environ.get("SHONAN_CONFIG_DIR", str(Path.home() / ".config" / "shonan-pi4")))
SETTINGS_PATH = SETTINGS_DIR / "settings.json"

# バンドごとの標準LO周波数(Hz)プロファイル。
BAND_PROFILES = {
    "BAND_1200": {"label_ja": "1200MHz帯", "label_en": "1200MHz Band", "lo_hz": 1_273_000_000,
                   "wifi": "2.4GHz/5GHz いずれも可", "wifi_reason": "RF帯域と重複しないため直接干渉なし", "bitrate_mbps": 1.5},
    "BAND_2400": {"label_ja": "2400MHz帯", "label_en": "2400MHz Band", "lo_hz": 2_407_000_000,
                   "wifi": "5GHz", "wifi_reason": "2.4GHz Wi-FiとRF帯域が重複するため", "bitrate_mbps": 1.5},
    "BAND_5600": {"label_ja": "5600MHz帯", "label_en": "5600MHz Band", "lo_hz": 5_730_000_000,
                   "wifi": "2.4GHz", "wifi_reason": "5GHz Wi-FiとRF帯域が重複するため", "bitrate_mbps": 1.5},
    "BAND_10000": {"label_ja": "10GHz帯", "label_en": "10GHz Band", "lo_hz": 10_180_000_000,
                   "wifi": "2.4GHz/5GHz いずれも可", "wifi_reason": "重複なし", "bitrate_mbps": 1.5},
    "BAND_24000": {"label_ja": "24GHz帯", "label_en": "24GHz Band", "lo_hz": 24_000_000_000,
                   "wifi": "2.4GHz/5GHz いずれも可", "wifi_reason": "重複なし", "bitrate_mbps": 1.5},
    "LOOPBACK": {"label_ja": "ループバック試験", "label_en": "Loopback Test", "lo_hz": None},
}

# 10GHz帯をLNBで受信するときの値。Langstoneの10GHz受信(langstone_config.py)と同じく、
# 表示10236.5MHz・LNB局部発振9750MHz(→Pluto受信486.5MHz)。LNBは受信専用。
LNB_LO_HZ = 9_750_000_000
LNB_DISPLAY_HZ = 10_236_500_000

FEC_RATES = ["1/4", "1/3", "2/5", "1/2", "3/5", "2/3", "3/4", "4/5", "5/6", "8/9", "9/10"]
# ★32APSKはTX_SUPPORTED_MODCODSに対応するFECが1つもない(実装なし)ため、
# 選択肢自体から除外する(選んでも必ず「未対応のMod-Cod組み合わせ」になるため)。
# 16APSKは運用対象外とし、選択肢・対応MOD-CODの両方から外した(Pi5版と同じ)。
MODULATION_SCHEMES = ["QPSK", "8PSK"]

# ETSI DVB-S2で定義される変調方式ごとの符号化率。Android版が公開する全選択肢を
# 実制御へ渡しつつ、標準にない組み合わせだけを開始前に拒否する。
MODULATION_FEC_RATES = {
    "QPSK": FEC_RATES,
    "8PSK": ["3/5", "2/3", "3/4", "5/6", "8/9", "9/10"],
}
# TX(Pluto内蔵変調器pluto_dvb、GUIから呼ぶ現行経路)とgr-dvbs2rx(RX,
# pi4/rx/shonan_rx.pyの_MODCOD_TABLE)の両方で実際に配線・検証済みのMOD-CODのみ。
# MODULATION_FEC_RATESはUI選択肢(ETSI規格上の全組み合わせ)を出すためのもので、
# ここでの絞り込みと混同しないこと。QPSK-S_1/2はpi5版と同じgr-dvbs2rx/pluto_dvb
# 経路で対応済み(旧aff3ct/tx_main.cppはconf/ファイル制約で1/2に対応していなかった
# が、GUIから廃止済みのため無関係)。
TX_SUPPORTED_MODCODS = [
    "QPSK-S_1/2", "QPSK-S_3/5", "QPSK-S_8/9", "8PSK-S_3/5", "8PSK-S_8/9",
]
RX_SUPPORTED_MODCODS = list(TX_SUPPORTED_MODCODS)


def supported_fec_rates(modulation: str) -> list[str]:
    """指定した変調方式でTX_SUPPORTED_MODCODSが実際に対応するFEC符号化率一覧。

    FEC画面(screens/fec.py)の選択肢を、開始時に拒否される組み合わせを
    含まないよう絞り込むために使う。
    """
    prefix = f"{modulation}-S_"
    return [combo[len(prefix):] for combo in TX_SUPPORTED_MODCODS if combo.startswith(prefix)]


SYMBOL_RATE_CANDIDATES_MSPS = [0.25, 0.333, 0.5, 0.666, 1.0, 2.0]

TX_VIDEO_BITRATE_BPS = 400_000
TX_AUDIO_BITRATE_BPS = 16_000
# 送信音声の入力。camera=USBカメラ内蔵マイク、usb=USBオーディオ(外付けマイク等)。
TX_AUDIO_INPUTS = ("camera", "usb")


def normalize_pluto_host(value: str) -> str:
    """Pluto接続先を正規化し、空白や制御文字を拒否する。"""
    host = str(value).strip()
    if host.startswith("ip:"):
        host = host[3:].strip()
    if not host or any(ord(char) < 32 or char.isspace() for char in host):
        raise ValueError("Pluto接続先に空白または制御文字が含まれています")
    try:
        ipaddress.ip_address(host)
        return host
    except ValueError:
        if len(host) <= 253 and re.fullmatch(r"[A-Za-z0-9.-]+", host):
            return host
        raise ValueError("Pluto接続先が不正です")


def normalize_ptt_controller_host(value: str) -> str:
    """Return a safe PTT controller (ESP32+W5500) host, or "" to disable the feature."""
    host = str(value).strip()
    if not host:
        return ""
    if any(ord(char) < 32 or char.isspace() for char in host):
        raise ValueError("PTTコントローラ接続先に空白または制御文字が含まれています")
    try:
        ipaddress.ip_address(host)
        return host
    except ValueError:
        if len(host) <= 253 and re.fullmatch(
                r"[A-Za-z0-9](?:[A-Za-z0-9.-]*[A-Za-z0-9])?", host):
            return host
    raise ValueError("PTTコントローラ接続先はIPアドレスまたはホスト名で入力してください")


@dataclass
class AppSettings:
    language: str = "JAPANESE"  # JAPANESE | ENGLISH

    selected_band: str = "BAND_1200"
    use_custom_lo_frequency: bool = True
    custom_lo_frequency_hz: int = 437_000_000
    # 周波数画面で10GHz帯を選んだときの「LNBを使用する」。ONの間は画面の周波数を
    # 10GHz表示のまま扱い、受信時だけLNB局部発振(LNB_LO_HZ)を引いてPlutoへ渡す。
    use_lnb: bool = False

    # Pluto+接続(Pi4はローカル直結のためURI形式。Android版のtxDestinationIP/Port相当を代替)
    pluto_uri: str = "ip:192.168.0.10"

    # PA_Power/PTTコントローラ(ESP32+W5500、hardware/W5500_PA_PTT_Control)のIPアドレス。
    # 空文字なら連携しない(未接続環境でもTX/RXの動作に影響しない)。
    ptt_controller_host: str = "192.168.0.100"
    # 設定画面の「ESP32 W5500を使用する」。OFFならIPアドレスを保持したまま連携しない。
    use_ptt_controller: bool = True
    tx_destination_port: int = 7272
    rx_listen_port: int = 4003
    rx_status_port: int = 4002
    rx_volume: float = 0.3  # 0.0..1.0 (初期音量30%)
    tmp_dir: str = "/tmp"

    # Android版と同じソフトウェアループ試験設定
    loopback_use_localhost: bool = False
    loopback_target_ip: str = "192.168.0.21"
    simultaneous_tx_rx_test: bool = False

    # GUI起動時およびRX開始直前にPluto RX DMAの短い読出し試験を行う。
    # 通常運用では不要なため既定はOFF。障害切り分け時に設定画面でONにする。
    iio_preflight_enabled: bool = False

    # 映像ソース(Android VideoSourceOption相当)
    camera_device: str = "/dev/video0"
    video_source: str = "colorbar"  # camera | file | colorbar
    video_file_path: str = ""
    use_color_bar_source: bool = True
    audio_enabled: bool = False
    # 送信音声の入力(TX_AUDIO_INPUTSのいずれか)。映像ソースとは独立に設定画面で選ぶ。
    # 選んだ側のデバイスが見つからない場合は無音で送信する(もう一方へは切り替えない)。
    tx_audio_input: str = "camera"
    # 送信音量(マイク録音音量、0..100%)。入力ごとに保存し、送信開始時にALSAミキサーへ反映する。
    # 送信中(オンデバイス復調OFF)にロータリーエンコーダを回すと変更できる。
    tx_audio_volume_camera: int = 80
    tx_audio_volume_usb: int = 80

    # カメラ映像へ焼き込むオーバーレイ(shonan_lite-ipad版CameraOverlayRenderer相当)。
    # コールサイン(左上・大)+送信開始時の日時と備考(右下・小)。カラーバーには
    # 焼き込まない(カラーバー画像自体に既にコールサインが描かれているため)。
    overlay_callsign: str = ""
    overlay_note: str = ""
    # 文字サイズ(px、1920x1080の送信映像上での大きさ)。映像ソース画面で選択する。
    overlay_callsign_font_size: int = 68
    overlay_note_font_size: int = 24
    # コールサイン・備考の文字色("#RRGGBB")。映像ソース画面で選択する。
    overlay_callsign_color: str = "#FFFFFF"
    overlay_note_color: str = "#FFFFFF"

    # RXゲイン
    rx_agc_enabled: bool = False
    rx_gain_db: int = 60  # 0..73、AGC OFF時のみ有効

    # TX出力
    tx_power_db: float = 0.0  # -70..0、0=最大出力（40 dB外部アッテネータ試験の既定）

    # FEC+Modulationの合成がmod_cod()。symbol_rate_mspsはRXへ実際に渡す。
    symbol_rate_msps: float = 0.5
    fec_rate: str = "3/5"
    modulation_scheme: str = "QPSK"
    use_on_device_demod: bool = False
    # RSSI測定: True=「検索停止」が押されるまで繰り返す(連続)、False=範囲の終わりまで1回で自動停止
    rssi_repeat_scan: bool = True

    # RFループバック自己申告フラグ(Android版のRF loopback警告と同じ、インターロックなし)
    rf_loopback_enabled: bool = False

    # ユーザー登録プリセット。各要素は表示名(name)と設定値(values)を持つ。
    presets: list[dict] = field(default_factory=list)

    def effective_lo_hz(self) -> Optional[int]:
        if self.use_custom_lo_frequency:
            return self.custom_lo_frequency_hz
        # 10GHz帯をLNB使用で選んだ場合は、バンド既定値ではなくLNB用の表示周波数。
        if self.use_lnb and self.selected_band == "BAND_10000":
            return LNB_DISPLAY_HZ
        # Android版effectiveLoHzと同じくLOOPBACKでは手動値へフォールバックする。
        return BAND_PROFILES[self.selected_band]["lo_hz"] or self.custom_lo_frequency_hz

    def lnb_active(self) -> bool:
        """LNB使用中(受信専用)か。周波数がLNB局部発振より上のときだけ有効。"""
        lo_hz = self.effective_lo_hz()
        return self.use_lnb and lo_hz is not None and lo_hz > LNB_LO_HZ

    def rx_tune_hz(self, display_hz: Optional[int] = None) -> Optional[int]:
        """画面表示の周波数から、受信時にPlutoへ設定する周波数を返す。

        LNB使用中は表示周波数からLNB局部発振を引く(10236.5MHz→486.5MHz)。
        """
        if display_hz is None:
            display_hz = self.effective_lo_hz()
        if display_hz is None:
            return None
        return display_hz - LNB_LO_HZ if self.lnb_active() else display_hz

    def tx_audio_volume(self) -> int:
        """選択中の送信音声の入力の送信音量(%)。"""
        if self.tx_audio_input == "usb":
            return self.tx_audio_volume_usb
        return self.tx_audio_volume_camera

    def set_tx_audio_volume(self, percent: int) -> None:
        if self.tx_audio_input == "usb":
            self.tx_audio_volume_usb = percent
        else:
            self.tx_audio_volume_camera = percent

    def is_loopback(self) -> bool:
        return self.selected_band == "LOOPBACK"

    def effective_loopback_host(self) -> str:
        return "127.0.0.1" if self.loopback_use_localhost else self.loopback_target_ip

    def active_ptt_controller_host(self) -> str:
        """PTTコントローラ連携に使う接続先。未使用設定またはIP未設定なら""。"""
        return self.ptt_controller_host if self.use_ptt_controller else ""

    def mod_cod(self) -> str:
        """FEC + Modulation を合成した --mod-cod 文字列(aff3ct/gr-dvbs2rx共通の命名)。"""
        return f"{self.modulation_scheme}-S_{self.fec_rate}"

    def pluto_host(self) -> str:
        return self.pluto_uri[3:] if self.pluto_uri.startswith("ip:") else self.pluto_uri

    def symbol_rate_hz(self) -> int:
        return round(self.symbol_rate_msps * 1_000_000)

    def tx_mod_cod_supported(self) -> bool:
        return self.mod_cod() in TX_SUPPORTED_MODCODS

    def rx_mod_cod_supported(self) -> bool:
        return self.mod_cod() in RX_SUPPORTED_MODCODS


def load() -> AppSettings:
    if not SETTINGS_PATH.exists():
        return AppSettings()
    try:
        data = json.loads(SETTINGS_PATH.read_text(encoding="utf-8"))
        defaults = asdict(AppSettings())
        defaults.update({k: v for k, v in data.items() if k in defaults})
        if defaults.get("use_color_bar_source"):
            defaults["video_source"] = "colorbar"
        elif defaults.get("video_source") == "colorbar":
            defaults["use_color_bar_source"] = True
        if defaults.get("tx_audio_input") not in TX_AUDIO_INPUTS:
            defaults["tx_audio_input"] = AppSettings.tx_audio_input
        for key in ("tx_audio_volume_camera", "tx_audio_volume_usb"):
            value = defaults.get(key)
            if not isinstance(value, int) or not 0 <= value <= 100:
                defaults[key] = getattr(AppSettings, key)
        try:
            defaults["ptt_controller_host"] = normalize_ptt_controller_host(
                defaults.get("ptt_controller_host", ""))
        except (TypeError, ValueError):
            defaults["ptt_controller_host"] = AppSettings.ptt_controller_host
        # 選択肢から外した変調方式(16APSK等)で保存された設定はQPSKへ移行し、
        # FECもQPSKで使えない値なら既定値へ戻す(Pi5版と同じ)。
        if defaults.get("modulation_scheme") not in MODULATION_SCHEMES:
            defaults["modulation_scheme"] = AppSettings.modulation_scheme
            if defaults.get("fec_rate") not in supported_fec_rates(defaults["modulation_scheme"]):
                defaults["fec_rate"] = AppSettings.fec_rate
        return AppSettings(**defaults)
    except (json.JSONDecodeError, OSError, TypeError):
        return AppSettings()


def save(settings: AppSettings) -> None:
    SETTINGS_DIR.mkdir(parents=True, exist_ok=True)
    SETTINGS_PATH.write_text(json.dumps(asdict(settings), indent=2, ensure_ascii=False), encoding="utf-8")
